VU-Civic/hardware/part_3d_cads/NCP186AMX180TAG.step

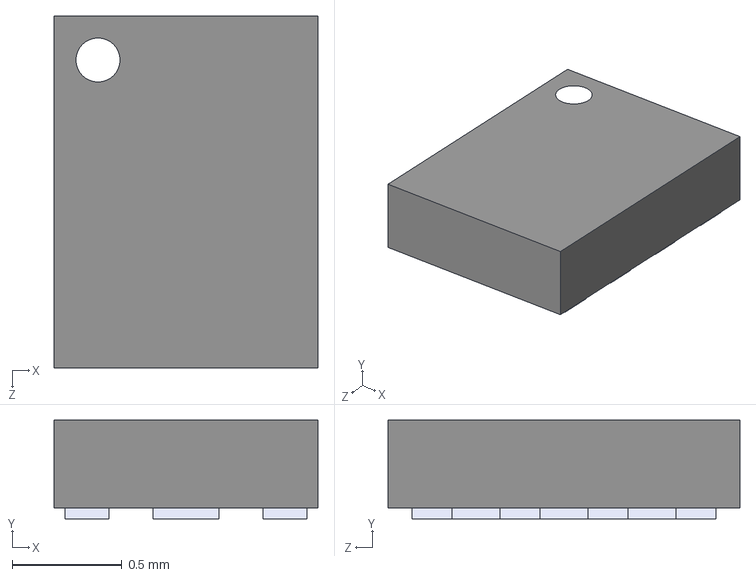
[picture p19: CAD file, 2025-09-10]
part_3d_cads/NCP186AMX180TAG.step
1.20 x 0.45 x 1.60 mm
