VU-Civic/hardware/part_3d_cads/KC2016Z48.0000C15XXK.step

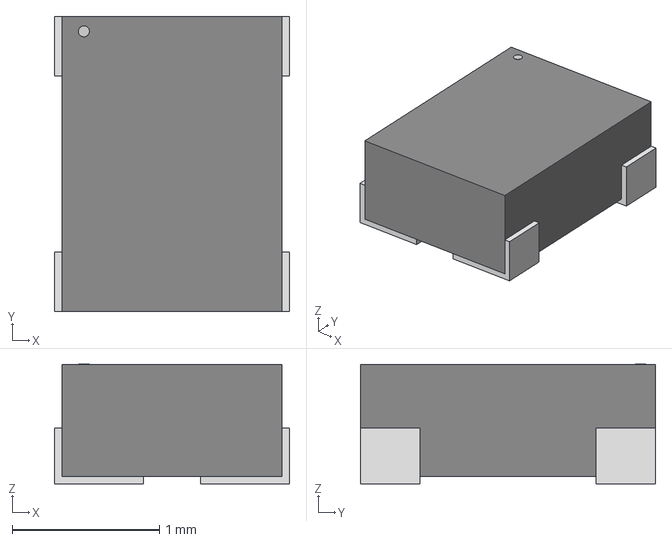
[picture p20: CAD file, 2025-09-10]
part_3d_cads/KC2016Z48.0000C15XXK.step
1.60 x 2.01 x 0.815 mm
