VU-Civic/hardware/part_3d_cads/SGECL01-01-1000.step

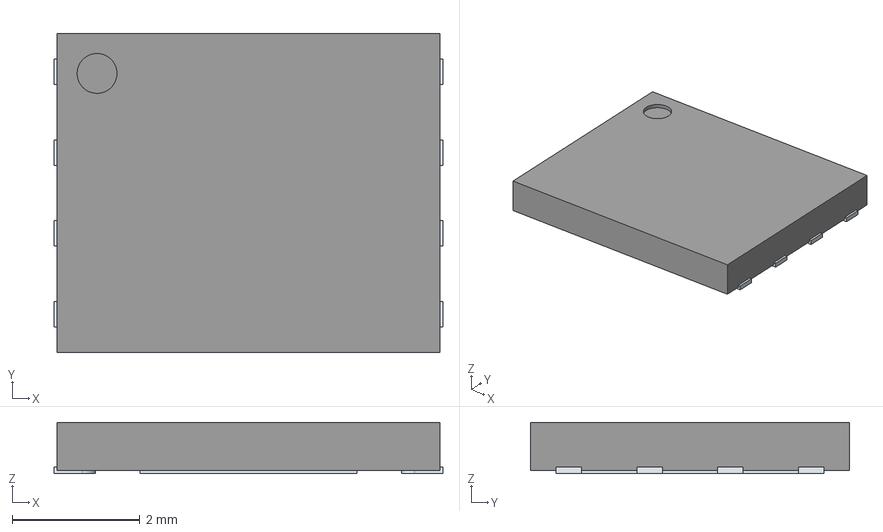
[picture p21: CAD file, 2025-06-16]
part_3d_cads/SGECL01-01-1000.step
6.10 x 5.00 x 0.8 mm
ThermalPin
PinsArrayLR
