VU-Civic/hardware/part_3d_cads/T520B337M006ATE040.step

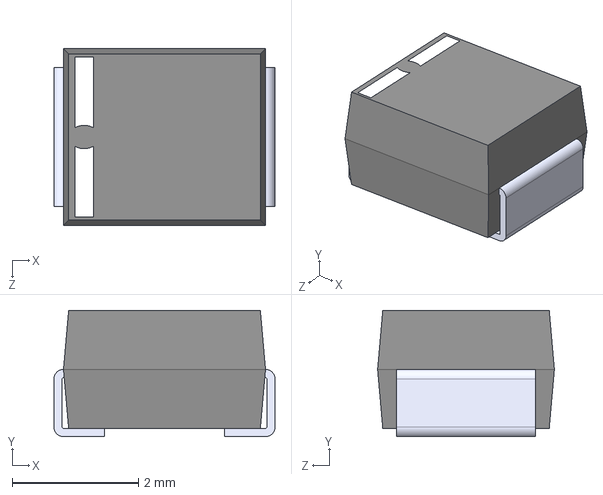
[picture p22: CAD file, 2025-06-16]
part_3d_cads/T520B337M006ATE040.step
3.50 x 2.00 x 2.80 mm
