VU-Civic/hardware/part_3d_cads/PESD0402-140_LTF.step

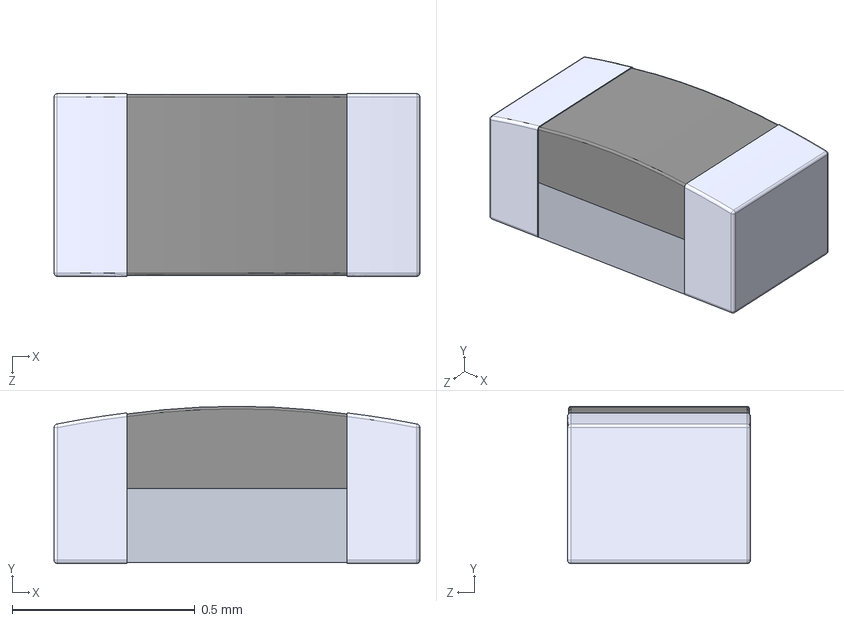
[picture p23: CAD file, 2025-06-16]
part_3d_cads/PESD0402-140_LTF.step
1.00 x 0.43 x 0.5 mm
