VU-Civic/hardware/part_3d_cads/BC847CE6327HTSA1.step

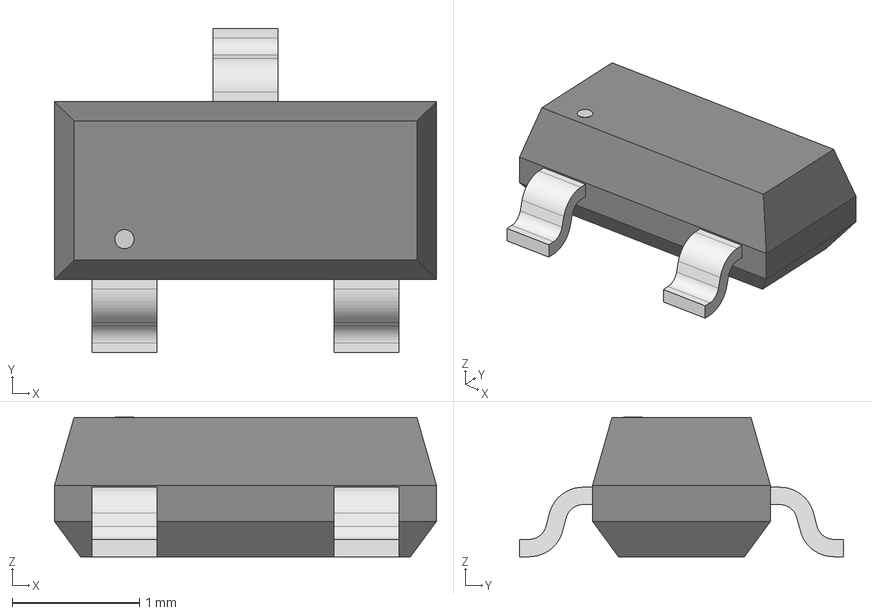
[picture p24: CAD file, 2025-06-16]
part_3d_cads/BC847CE6327HTSA1.step
3.00 x 2.54 x 1.09 mm
