VU-Civic/hardware/part_3d_cads/NCP186BMX185TAG.step

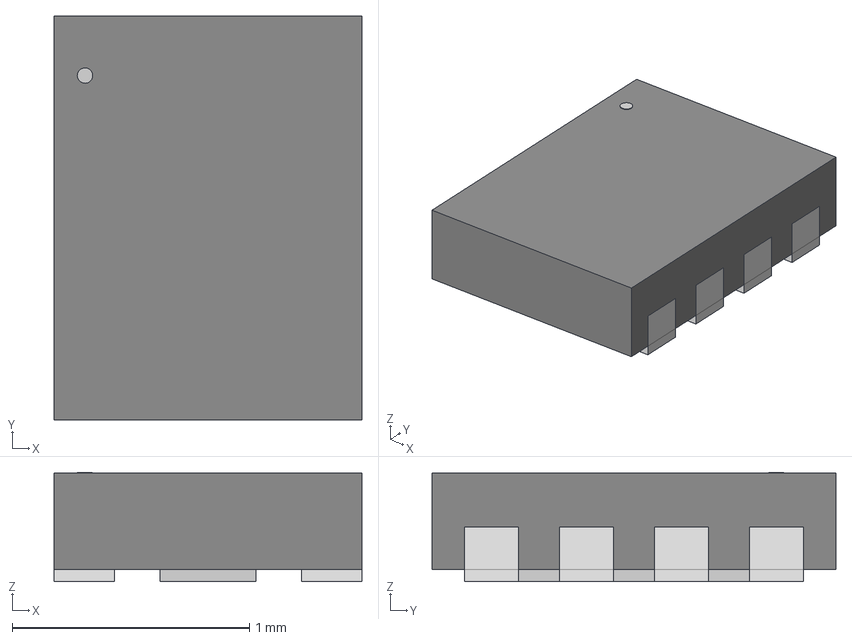
[picture p25: CAD file, 2025-06-16]
part_3d_cads/NCP186BMX185TAG.step
1.30 x 1.70 x 0.46 mm
