VU-Civic/hardware/part_3d_cads/BLM18EG221SN1D.step

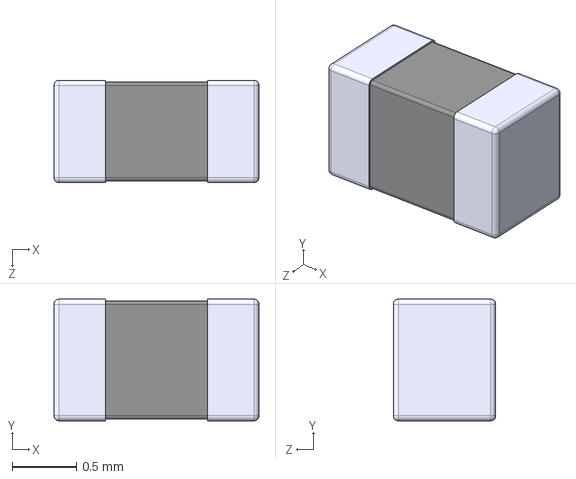
[picture p26: CAD file, 2025-06-16]
part_3d_cads/BLM18EG221SN1D.step
1.60 x 0.95 x 0.8 mm
