VU-Civic/hardware/part_3d_cads/RECE.20279.001E.01.step

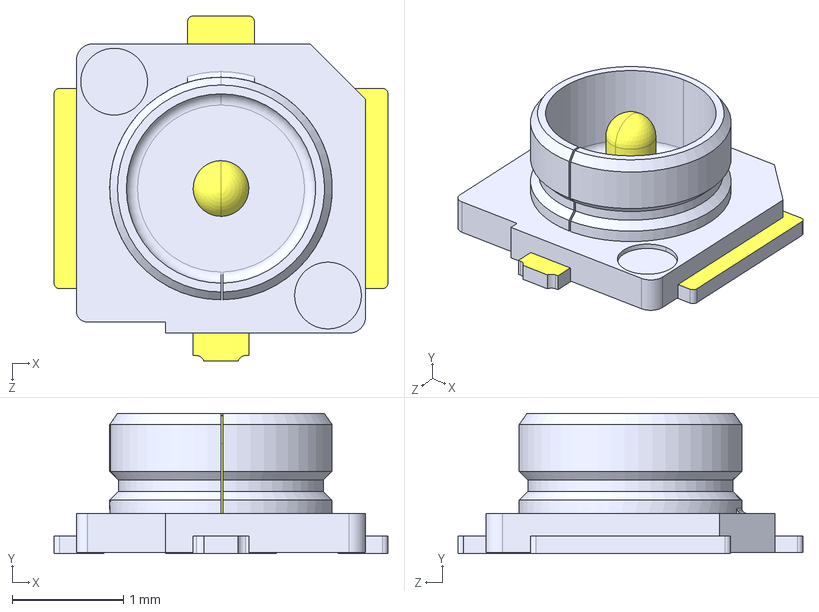
[picture p27: CAD file, 2025-06-16]
part_3d_cads/RECE.20279.001E.01.step
3.00 x 1.26 x 3.10 mm
