VU-Civic/hardware/part_3d_cads/ICM-20948.step

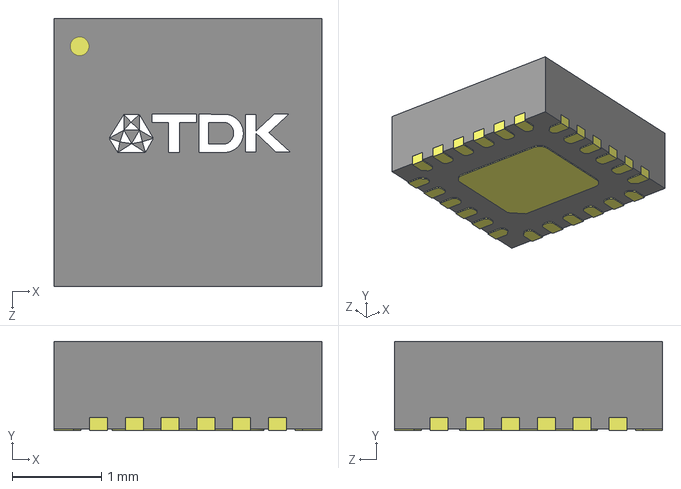
[picture p28: CAD file, 2025-06-16]
part_3d_cads/ICM-20948.step
3.00 x 1.00 x 3.00 mm
