VU-Civic/hardware/part_3d_cads/ESDALC6V1W5.step

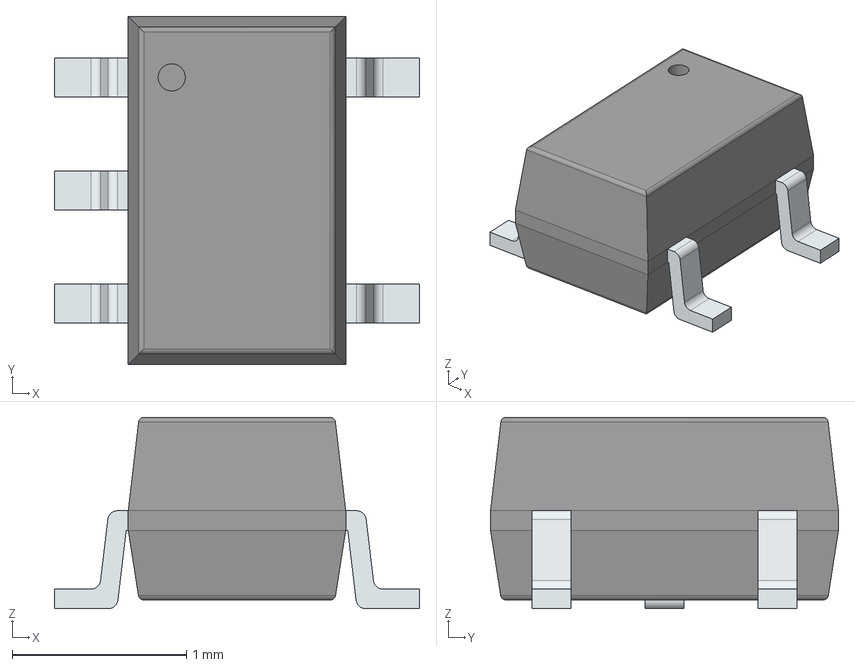
[picture p29: CAD file, 2025-06-16]
part_3d_cads/ESDALC6V1W5.step
2.10 x 2.00 x 1.10 mm
PinsArrayL
PinsArrayR
