VU-Civic/hardware/part_3d_cads/ATX-H11-F-25_000MHz-F25-T.step

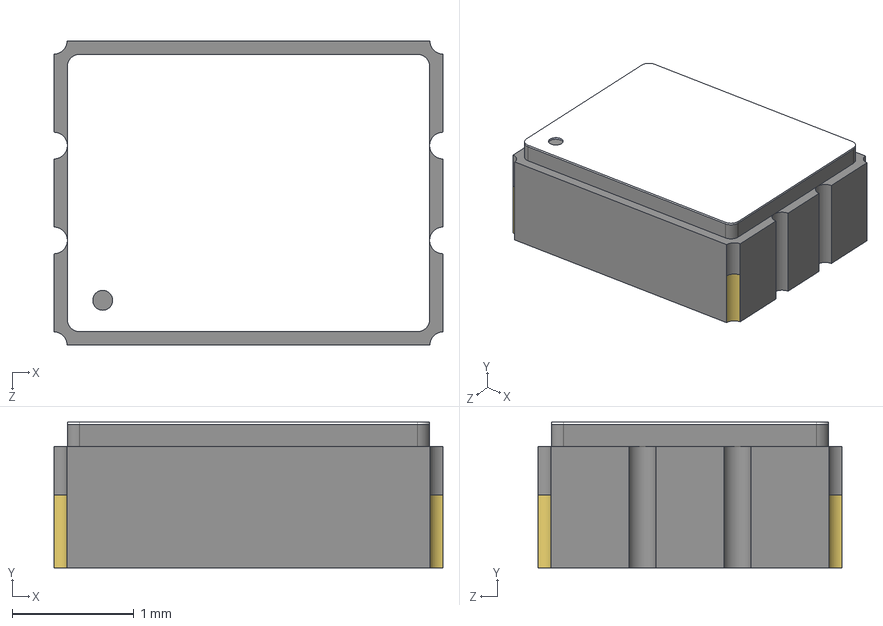
[picture p30: CAD file, 2025-06-16]
part_3d_cads/ATX-H11-F-25_000MHz-F25-T.step
3.20 x 1.20 x 2.50 mm
