VU-Civic/hardware/part_3d_cads/IM73D122V01XTMA1.step

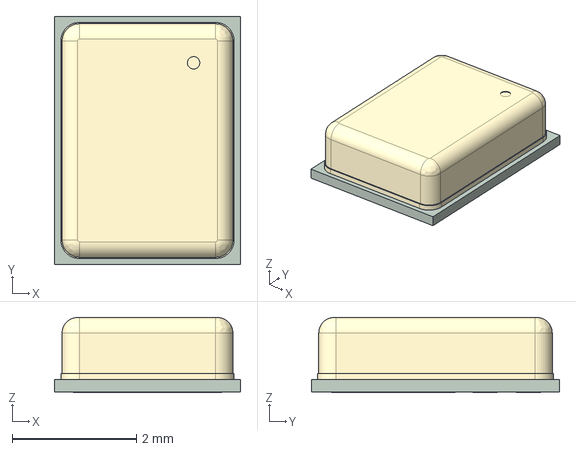
[picture p31: CAD file, 2025-06-16]
part_3d_cads/IM73D122V01XTMA1.step
3.00 x 4.00 x 1.21 mm
