VU-Civic/hardware/part_3d_cads/STM32H745ZIT6.step

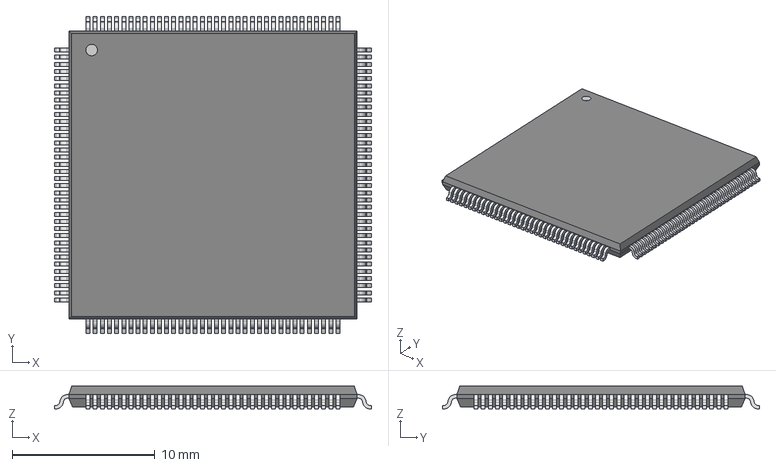
[picture p32: CAD file, 2025-06-16]
part_3d_cads/STM32H745ZIT6.step
22.2 x 22.2 x 1.60 mm
